Codesignseo/OBD2_Display_for_FordMustang_ESP32-S3/Images/3DPrints.jpg

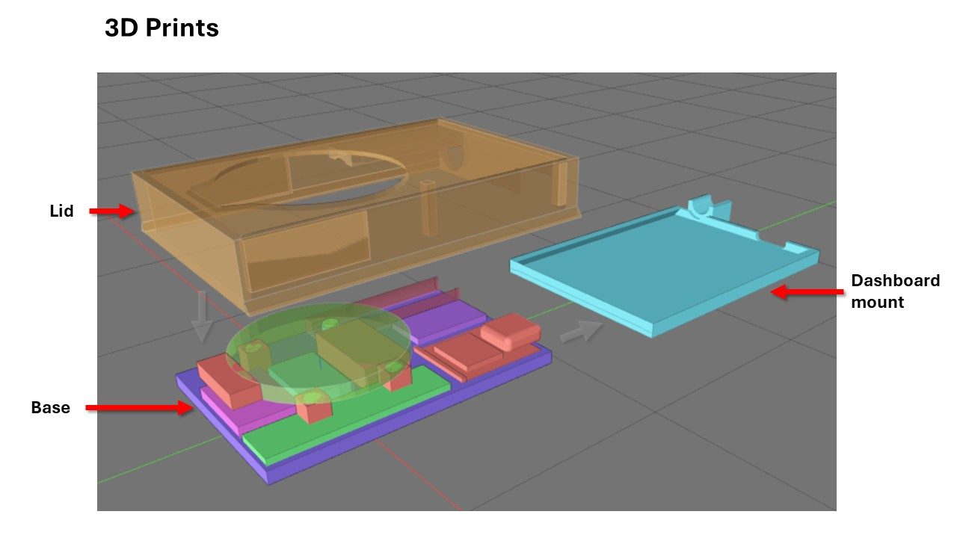
Images/3DPrints.jpg
