Codesignseo/OBD2_Display_for_FordMustang_ESP32-S3/Images/DashboardMount.jpg

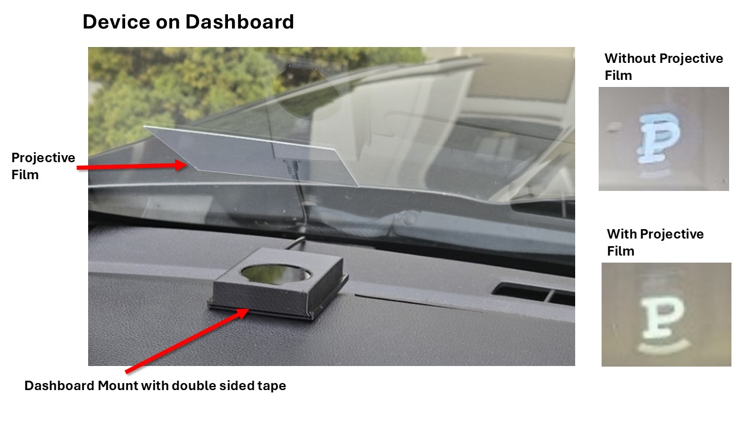
Images/DashboardMount.jpg
