Codesignseo/OBD2_Display_for_FordMustang_ESP32-S3/Images/GC9A01.jpg

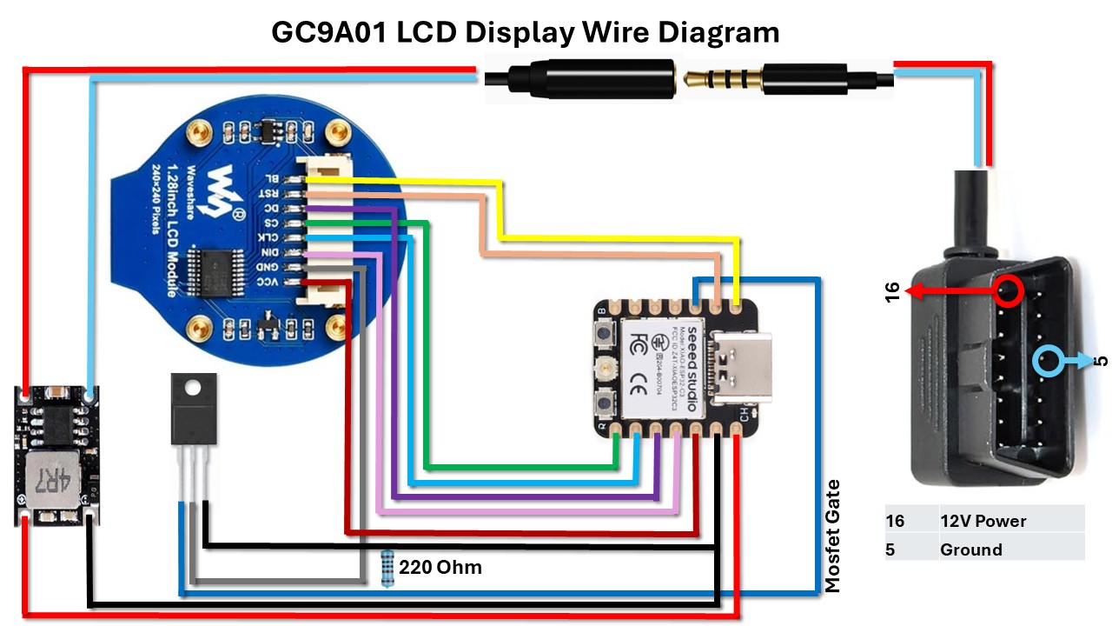
Images/GC9A01.jpg
