Codesignseo/OBD2_Display_for_FordMustang_ESP32-S3/Images/OBD2_Pins.jpg

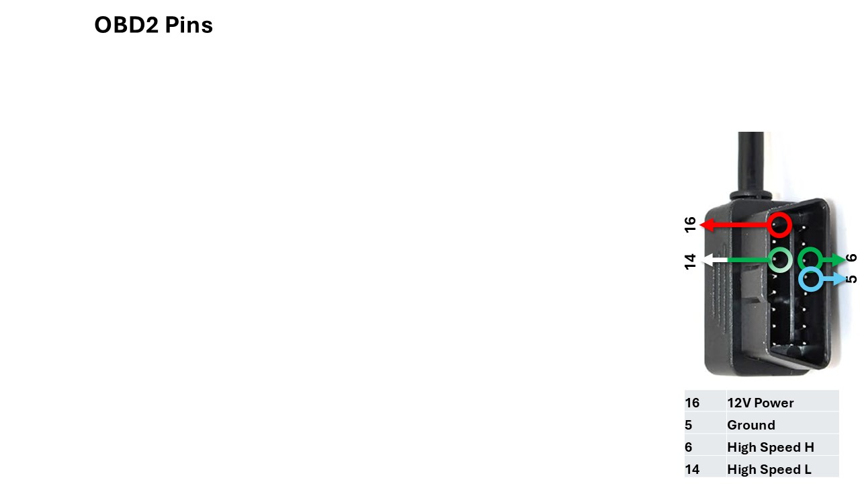
Images/OBD2_Pins.jpg
