Codesignseo/OBD2_Display_for_FordMustang_ESP32-S3/Images/SN65HVD230.jpg

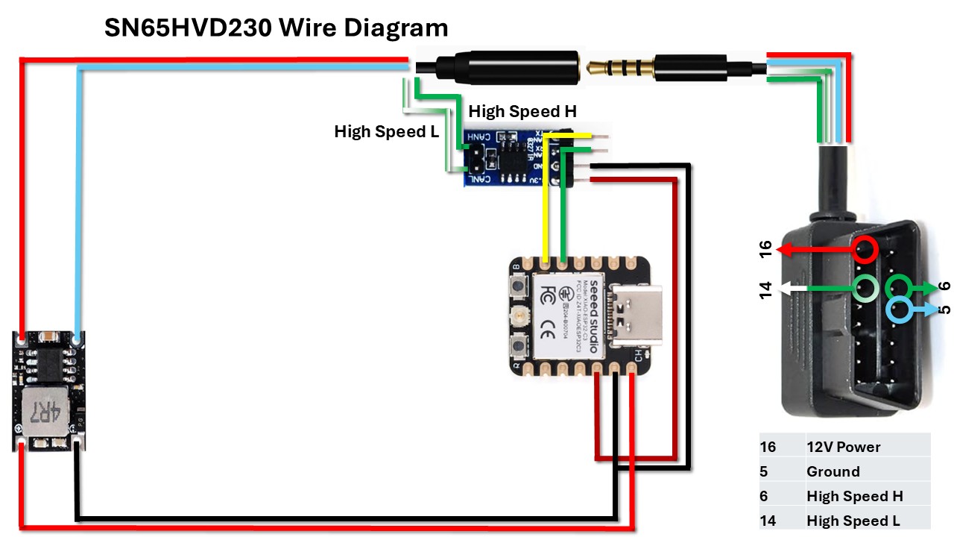
Images/SN65HVD230.jpg
