Codesignseo/OBD2_Display_for_FordMustang_ESP32-S3/FreeMonoBold54pt7b.h

#ifndef FreeMonoBold54pt7b_H
#define FreeMonoBold54pt7b_H

#ifdef __AVR__
#include <avr/io.h>
#include <avr/pgmspace.h>
#elif defined(ESP8266)
#include <pgmspace.h>
#undef PROGMEM
#define PROGMEM STORE_ATTR
#elif defined(__IMXRT1052__) || defined(__IMXRT1062__)
// PROGMEM is defefind for T4 to place data in specific memory section
#undef PROGMEM
#define PROGMEM
#else
#define PROGMEM
#endif

/*const*/ uint8_t FreeMonoBold54pt7bBitmaps[] PROGMEM = {
  0x00, 0x01, 0xC0, 0x07, 0xFC, 0x07, 0xFF, 0x07, 0xFF, 0xC7, 0xFF, 0xF3,
  0xFF, 0xFB, 0xFF, 0xFF, 0xFF, 0xFF, 0xFF, 0xFF, 0xFF, 0xFF, 0xFF, 0xFF,
  0xFF, 0xFF, 0xFF, 0xFF, 0xFF, 0xFF, 0xFF, 0xFF, 0xFE, 0xFF, 0xFE, 0x7F,
  0xFF, 0x3F, 0xFF, 0x9F, 0xFF, 0xCF, 0xFF, 0xE7, 0xFF, 0xF3, 0xFF, 0xF9,
  0xFF, 0xFC, 0xFF, 0xFE, 0x7F, 0xFF, 0x3F, 0xFF, 0x8F, 0xFF, 0x87, 0xFF,
  0xC3, 0xFF, 0xE1, 0xFF, 0xF0, 0xFF, 0xF8, 0x7F, 0xFC, 0x3F, 0xFE, 0x1F,
  0xFF, 0x0F, 0xFF, 0x87, 0xFF, 0xC1, 0xFF, 0xC0, 0xFF, 0xE0, 0x7F, 0xF0,
  0x3F, 0xF8, 0x1F, 0xFC, 0x0F, 0xFE, 0x07, 0xFF, 0x03, 0xFF, 0x81, 0xFF,
  0xC0, 0x7F, 0xC0, 0x3F, 0xE0, 0x0F, 0xE0, 0x03, 0xE0, 0x00, 0x00, 0x00,
  0x00, 0x00, 0x00, 0x00, 0x00, 0x00, 0x00, 0x00, 0x00, 0x00, 0x00, 0x00,
  0x07, 0xF0, 0x0F, 0xFE, 0x0F, 0xFF, 0x8F, 0xFF, 0xC7, 0xFF, 0xF3, 0xFF,
  0xF9, 0xFF, 0xFC, 0xFF, 0xFE, 0x7F, 0xFF, 0x3F, 0xFF, 0x9F, 0xFF, 0x87,
  0xFF, 0xC1, 0xFF, 0xC0, 0x3F, 0x80, 0xFF, 0xF8, 0x07, 0xFF, 0xDF, 0xFE,
  0x00, 0xFF, 0xF7, 0xFF, 0x80, 0x3F, 0xFD, 0xFF, 0xE0, 0x0F, 0xFF, 0x7F,
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
  { 12528,  59,  64,  64,    4,  -62 },   // 0x47 'G'
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

const GFXfont FreeMonoBold54pt7b PROGMEM = {
  (uint8_t  *)FreeMonoBold54pt7bBitmaps,
  (GFXglyph *)FreeMonoBold54pt7bGlyphs,
  0x20, 0x7E, 106 };

// Approx. 35251 bytes

#endif // FreeMonoBold54pt7b_H
